Xinyuan-LilyGO/T-Encoder-Pro/examples/UI_demo/port/lv_port_indev.h

/**
 * @file lv_port_indev_templ.h
 *
 */

/*Copy this file as "lv_port_indev.h" and set this value to "1" to enable content*/
#if 1

#ifndef LV_PORT_INDEV_TEMPL_H
#define LV_PORT_INDEV_TEMPL_H

#ifdef __cplusplus
extern "C" {
#endif

/*********************
 *      INCLUDES
 *********************/
#include "lvgl.h"

/*********************
 *      DEFINES
 *********************/

/**********************
 *      TYPEDEFS
 **********************/

/**********************
 * GLOBAL PROTOTYPES
 **********************/
void lv_port_indev_init(void);
void lv_indev_encode_en(bool en);
void lv_indev_touchpad_en(bool en);
void in_indev_touchpad_line_en(bool en);

/**********************
 *      MACROS
 **********************/

#ifdef __cplusplus
} /*extern "C"*/
#endif

#endif /*LV_PORT_INDEV_TEMPL_H*/

#endif /*Disable/Enable content*/
